clehn8ok/enderwire/STLs/badge_HR.stl

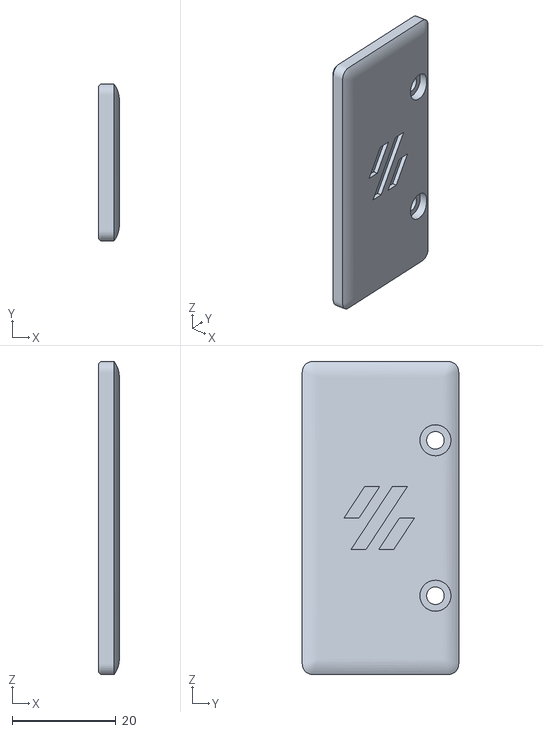
[picture p15: CAD file, 2022-12-23]
STLs/badge_HR.stl
4.00 x 30.2 x 60.4
