clehn8ok/enderwire/STLs/test_print_carriage.stl

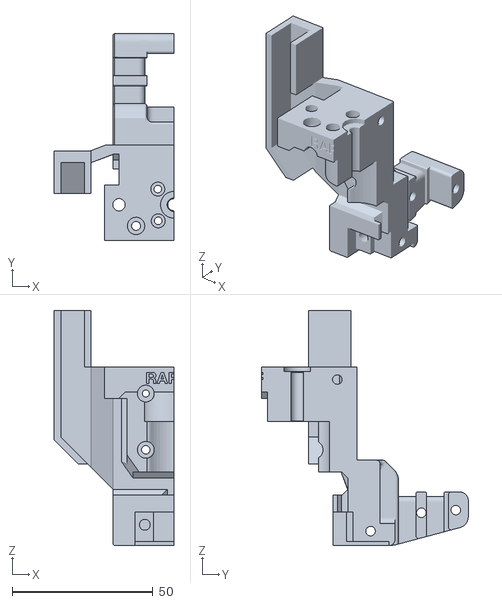
[picture p16: CAD file, 2022-12-23]
STLs/test_print_carriage.stl
42.6 x 73.4 x 83.5
