clehn8ok/enderwire/STLs/x_carriage_3.stl

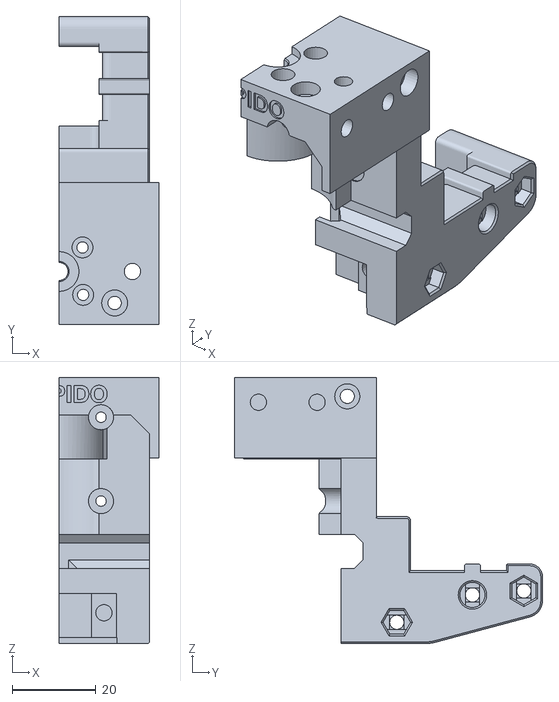
[picture p17: CAD file, 2022-12-23]
STLs/x_carriage_3.stl
23.8 x 73.4 x 63.5
