clehn8ok/enderwire/STLs/y_belt_clamp_K_X_F6RPER4-9665_.stl

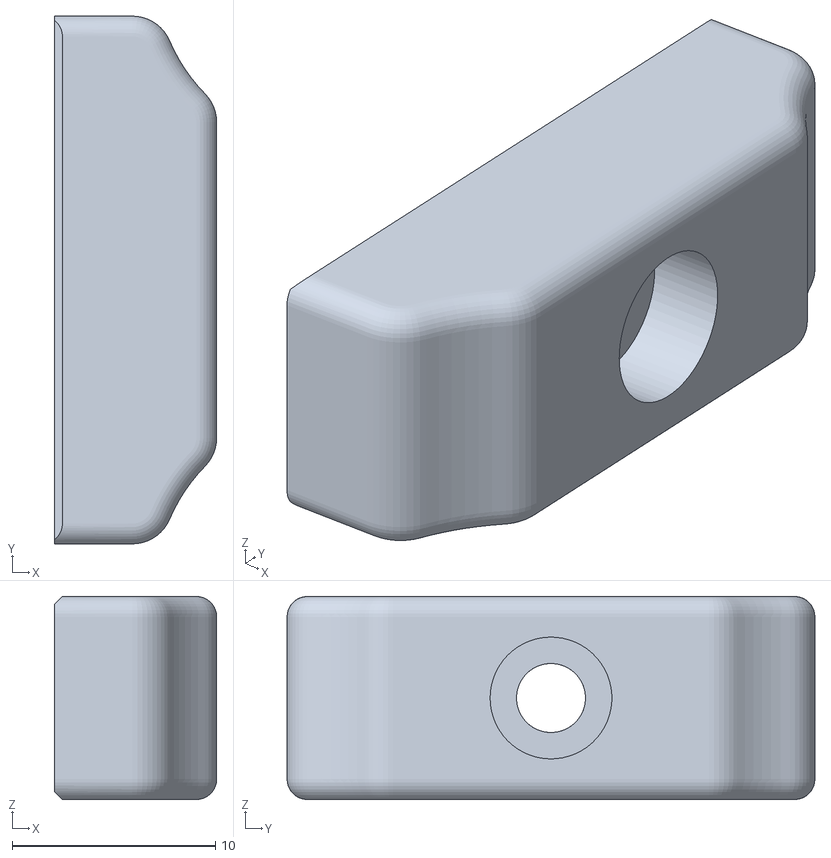
[picture p18: CAD file, 2022-12-23]
STLs/y_belt_clamp_K_X_F6RPER4-9665_.stl
8.00 x 26.0 x 10.0
