clehn8ok/enderwire/STLs/spoolHolder.stl

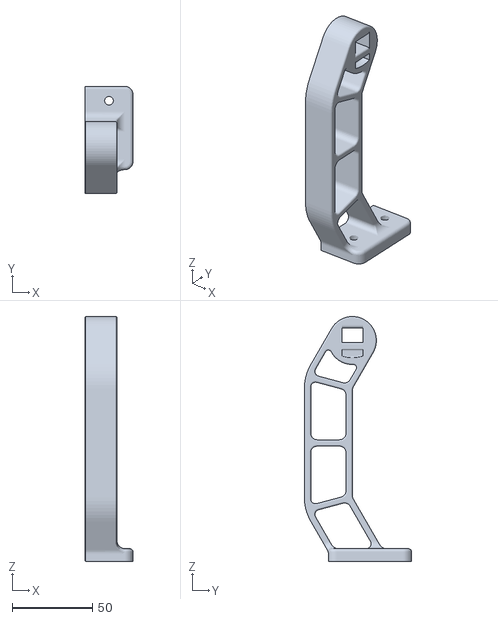
[picture p19: CAD file, 2022-12-23]
STLs/spoolHolder.stl
30.0 x 67.0 x 153.0
