clehn8ok/enderwire/STLs/side_extension_rightlang_hinten.stl

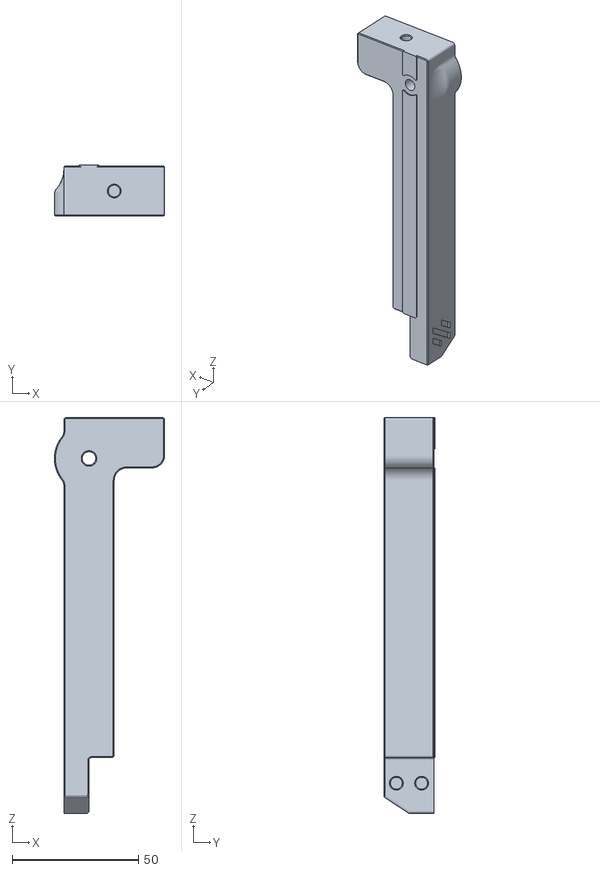
[picture p20: CAD file, 2022-12-23]
STLs/side_extension_rightlang_hinten.stl
43.8 x 20.4 x 157.1
