clehn8ok/enderwire/STLs/knob.stl

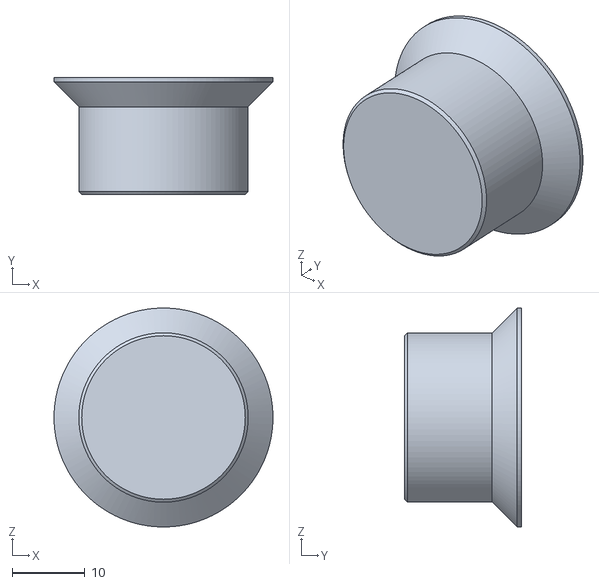
[picture p21: CAD file, 2022-12-23]
STLs/knob.stl
30.0 x 16.0 x 30.0
