clehn8ok/enderwire/STLs/xBlockLH.stl

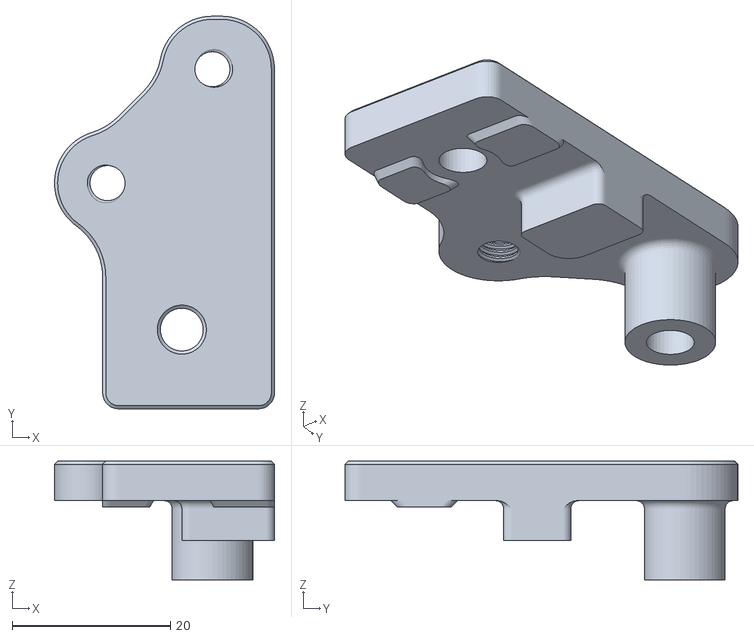
[picture p22: CAD file, 2022-12-23]
STLs/xBlockLH.stl
27.8 x 49.6 x 15.0
