clehn8ok/enderwire/STLs/front_grill_middle.stl

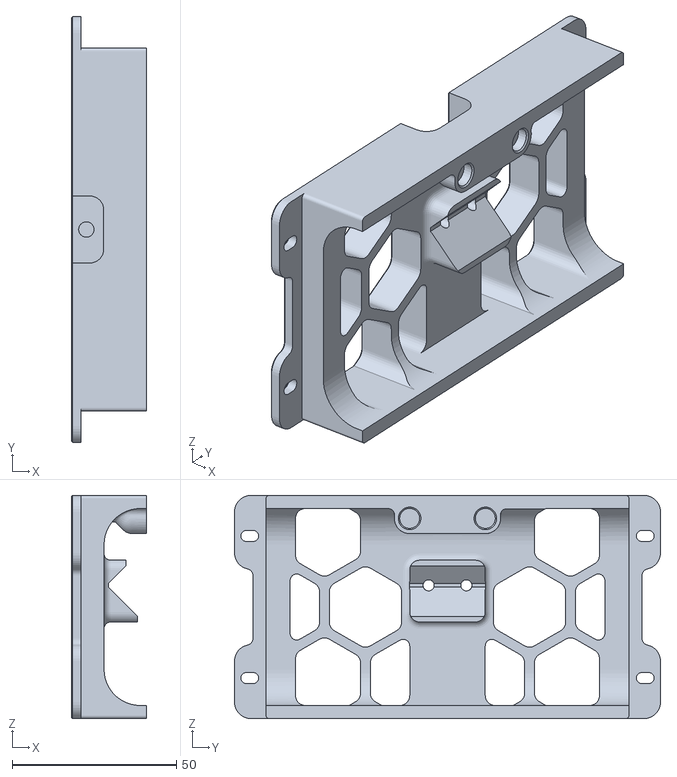
[picture p23: CAD file, 2022-12-23]
STLs/front_grill_middle.stl
23.0 x 129.8 x 68.0
