clehn8ok/enderwire/STLs/sideextension_leftfront.stl

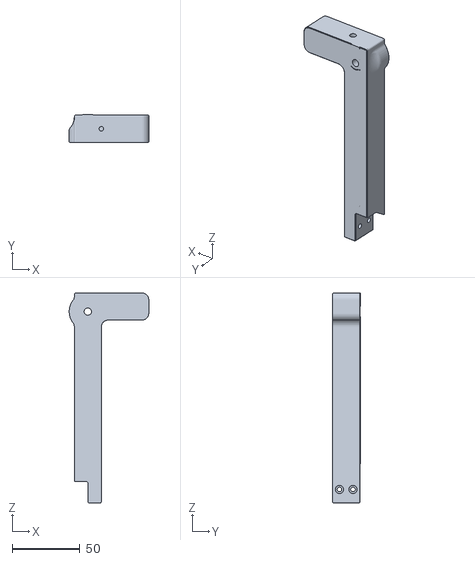
[picture p24: CAD file, 2022-12-23]
STLs/sideextension_leftfront.stl
58.7 x 20.4 x 154.9
