clehn8ok/enderwire/STLs/PI_bracket.stl

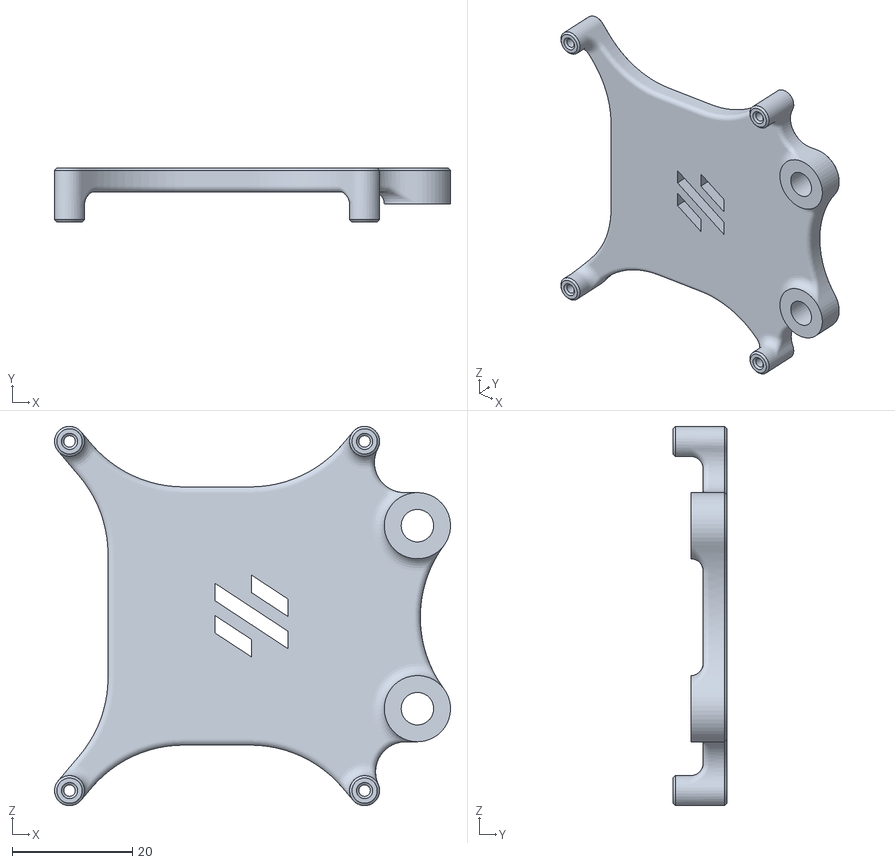
[picture p25: CAD file, 2022-12-23]
STLs/PI_bracket.stl
65.8 x 9.00 x 63.0
