clehn8ok/enderwire/STLs/psuMOunt1.stl

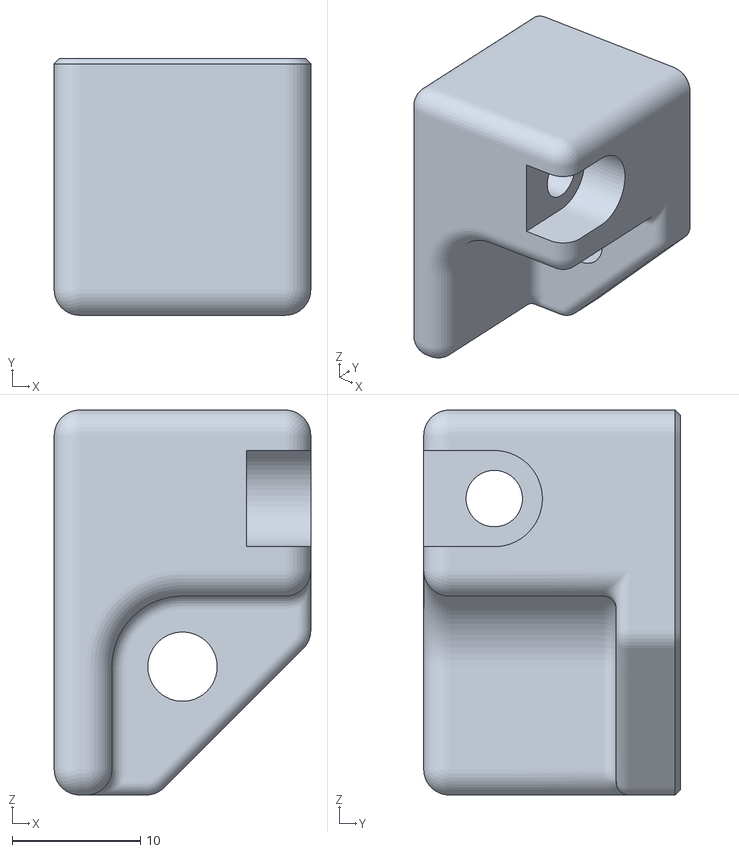
[picture p26: CAD file, 2022-12-23]
STLs/psuMOunt1.stl
20.0 x 20.0 x 30.0
