clehn8ok/enderwire/STLs/displayfront.stl

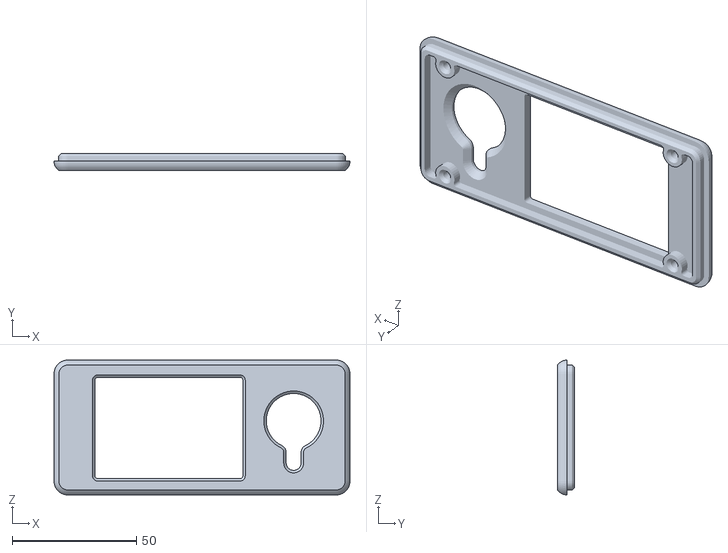
[picture p27: CAD file, 2022-12-23]
STLs/displayfront.stl
119.0 x 7.00 x 54.2
