clehn8ok/enderwire/STLs/connection_plateSideGrill.stl

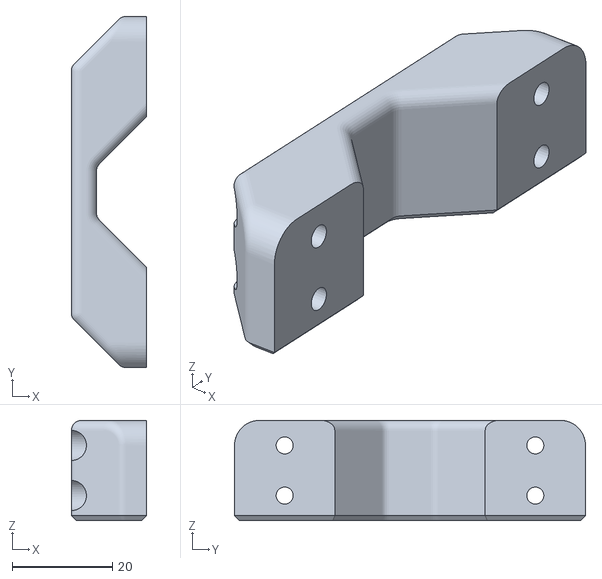
[picture p28: CAD file, 2022-12-23]
STLs/connection_plateSideGrill.stl
15.0 x 70.0 x 20.0
