clehn8ok/enderwire/STLs/zcarriageL.stl

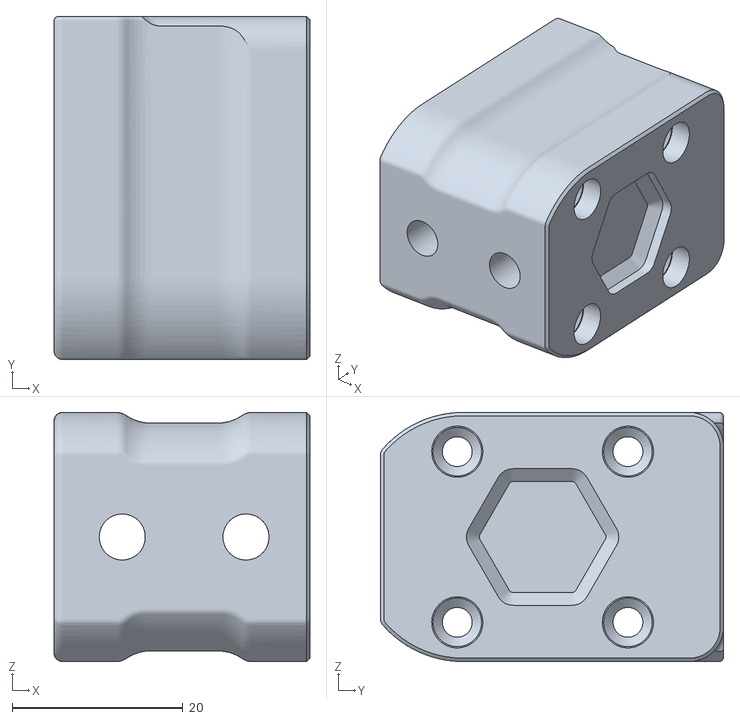
[picture p29: CAD file, 2022-12-23]
STLs/zcarriageL.stl
30.0 x 40.2 x 29.2
