clehn8ok/enderwire/STLs/fron_grill_connector.stl

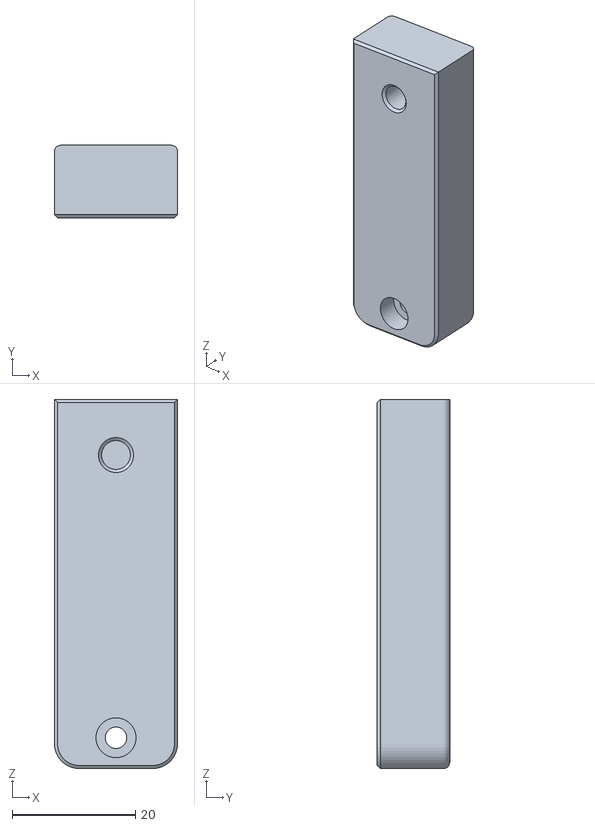
[picture p30: CAD file, 2022-12-23]
STLs/fron_grill_connector.stl
20.0 x 11.8 x 60.0
