clehn8ok/enderwire/STLs/zChainMount.stl

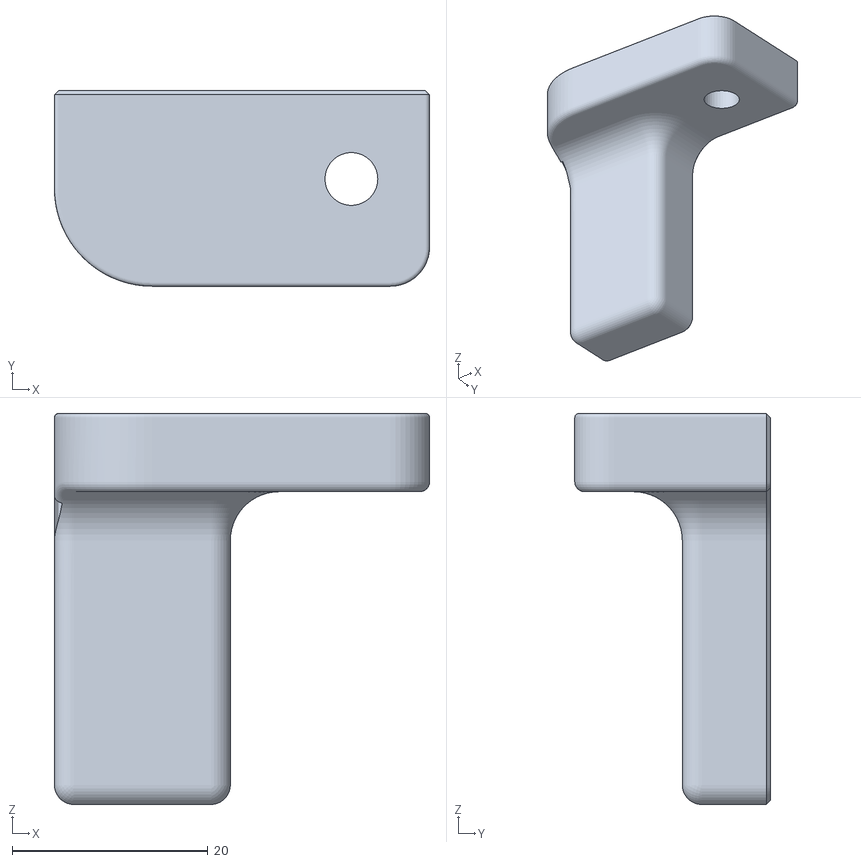
[picture p31: CAD file, 2022-12-23]
STLs/zChainMount.stl
38.4 x 20.0 x 40.0
