clehn8ok/enderwire/STLs/keybak1.stl

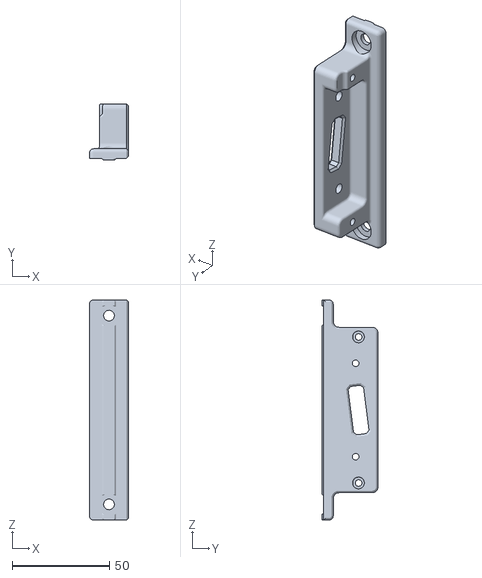
[picture p32: CAD file, 2022-12-23]
STLs/keybak1.stl
20.0 x 28.8 x 113.0
