clehn8ok/enderwire/STLs/displayback.stl

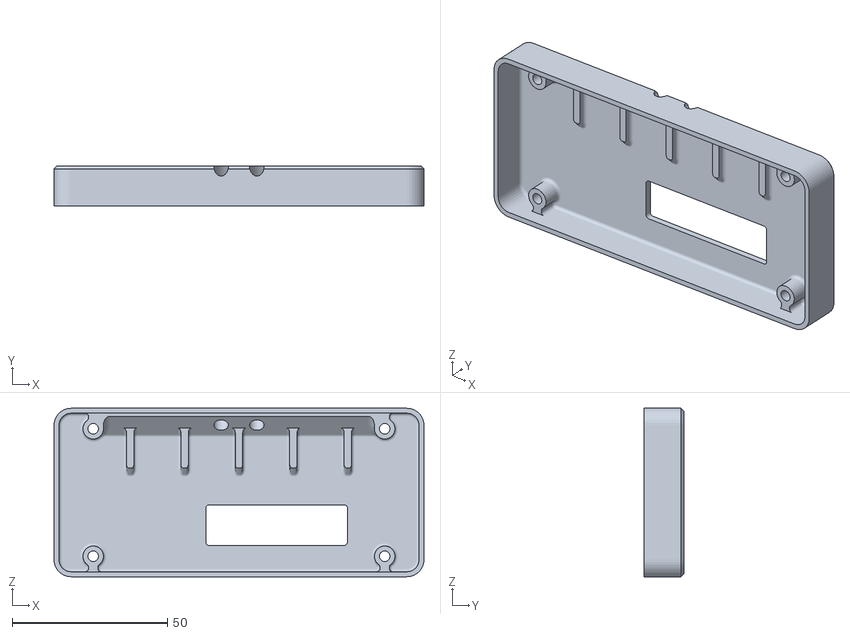
[picture p33: CAD file, 2022-12-23]
STLs/displayback.stl
119.0 x 13.0 x 54.2
