clehn8ok/enderwire/STLs/x_carriage_l.stl

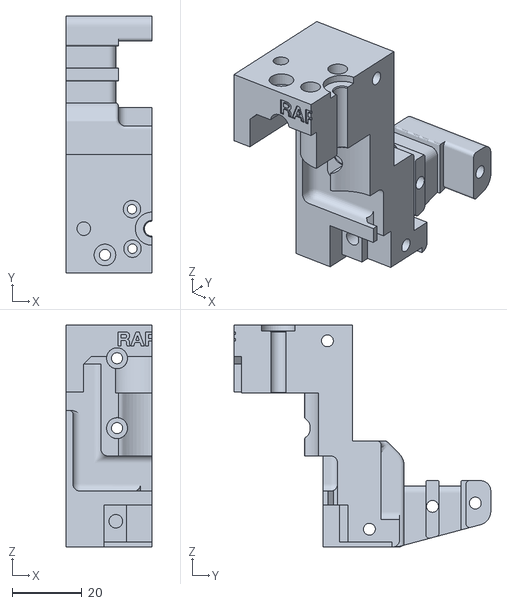
[picture p34: CAD file, 2022-12-23]
STLs/x_carriage_l.stl
24.6 x 73.4 x 63.5
