clehn8ok/enderwire/STLs/z_carriageR.stl

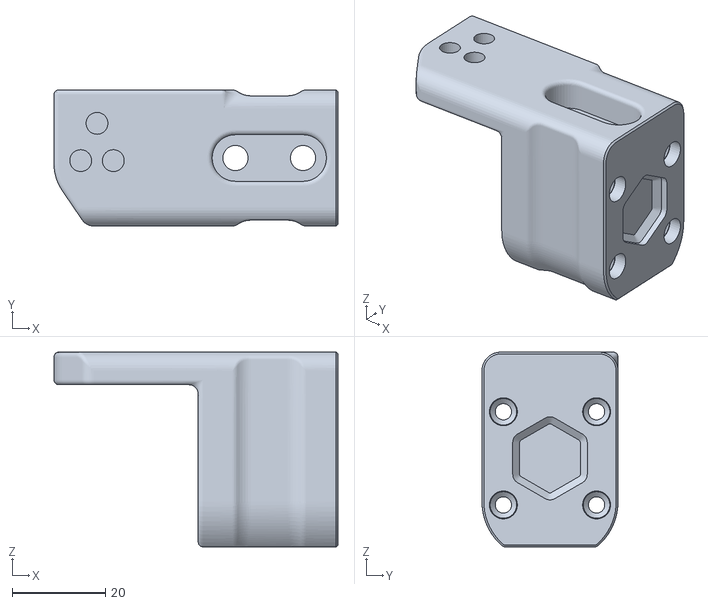
[picture p35: CAD file, 2022-12-23]
STLs/z_carriageR.stl
60.9 x 29.2 x 41.8
