clehn8ok/enderwire/STLs/hing1.stl

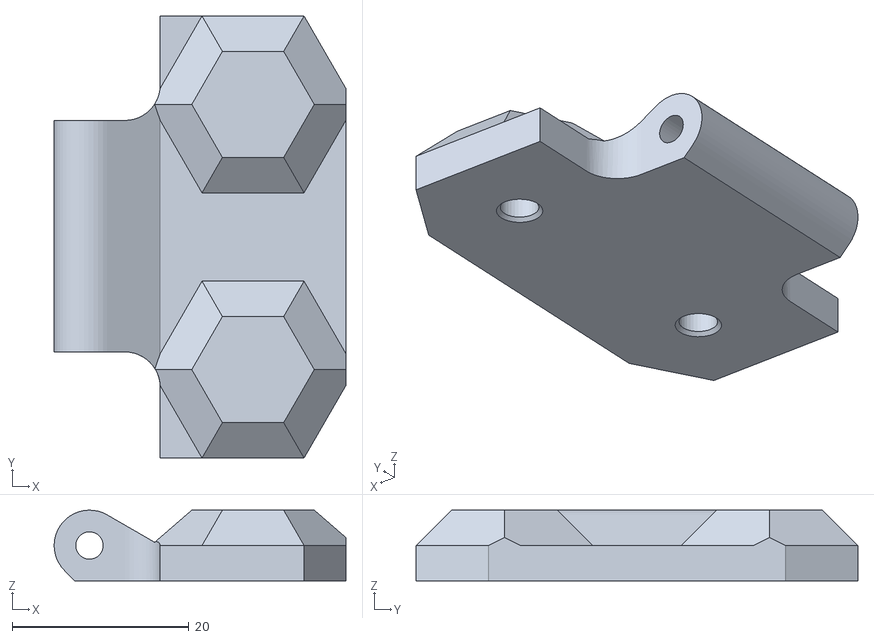
[picture p36: CAD file, 2022-12-23]
STLs/hing1.stl
33.0 x 50.0 x 8.00
