clehn8ok/enderwire/STLs/topDoorRightMagnet.stl

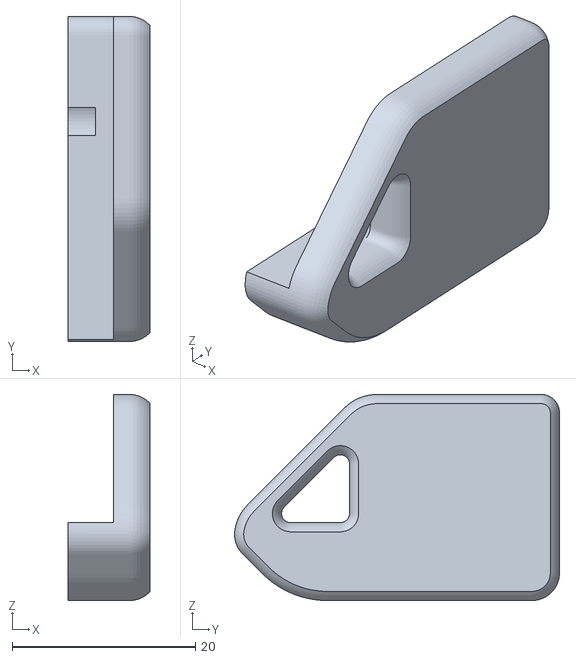
[picture p37: CAD file, 2022-12-23]
STLs/topDoorRightMagnet.stl
9.00 x 35.5 x 22.5
