clehn8ok/enderwire/STLs/side_extension_rightlang_vorne.stl

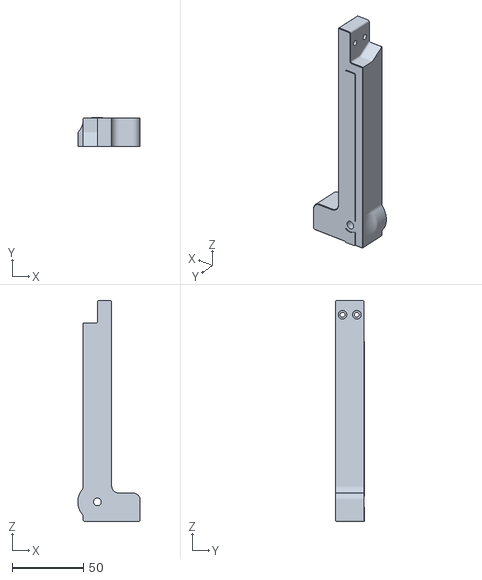
[picture p38: CAD file, 2022-12-23]
STLs/side_extension_rightlang_vorne.stl
43.8 x 20.4 x 154.9
