clehn8ok/enderwire/STLs/sideextension_rioghtfrontBreit_Vorne.stl

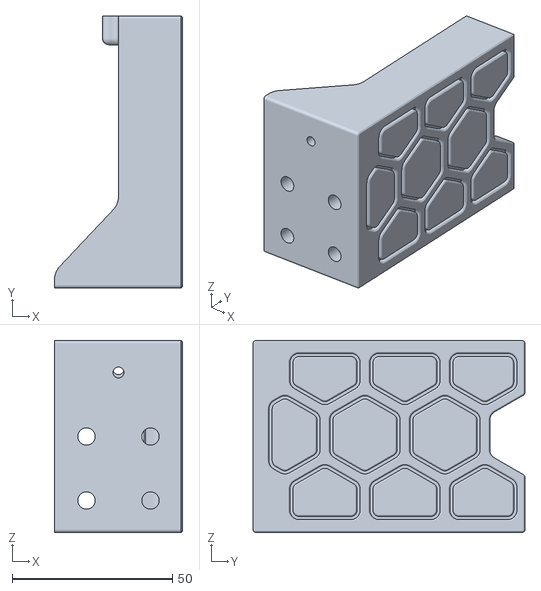
[picture p39: CAD file, 2022-12-23]
STLs/sideextension_rioghtfrontBreit_Vorne.stl
40.0 x 85.0 x 60.0
