clehn8ok/enderwire/STLs/y_axis_tensioner_K_X_F6RPER3-9642_.stl

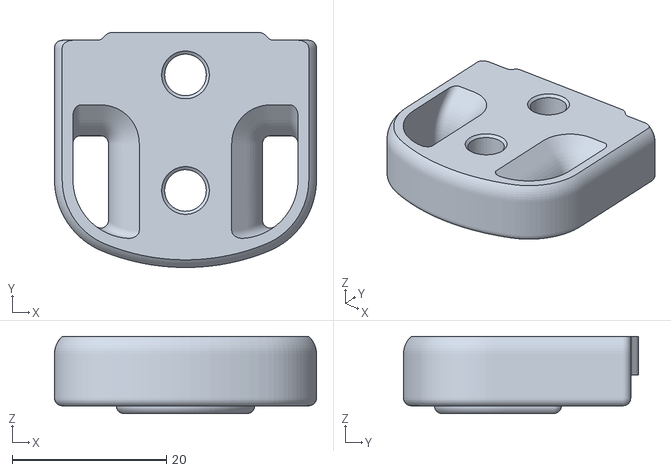
[picture p40: CAD file, 2022-12-23]
STLs/y_axis_tensioner_K_X_F6RPER3-9642_.stl
34.0 x 30.5 x 10.0
