clehn8ok/enderwire/STLs/ledHolder_upperright.stl

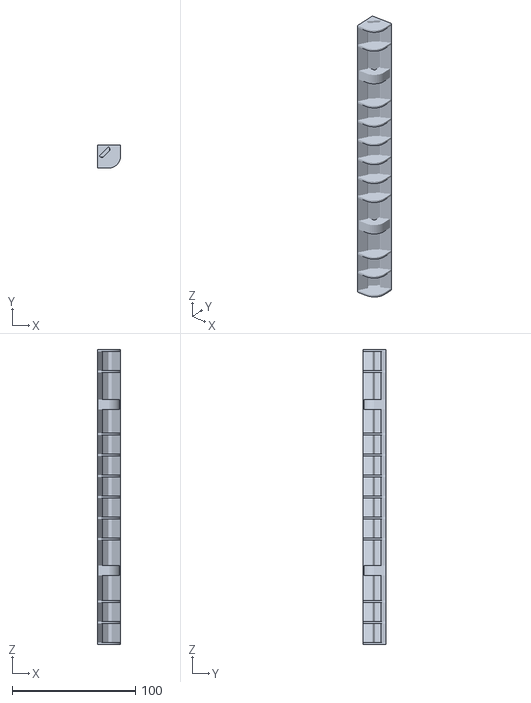
[picture p41: CAD file, 2022-12-23]
STLs/ledHolder_upperright.stl
19.0 x 19.0 x 239.6
