clehn8ok/enderwire/STLs/backacrylPanelHolder.stl

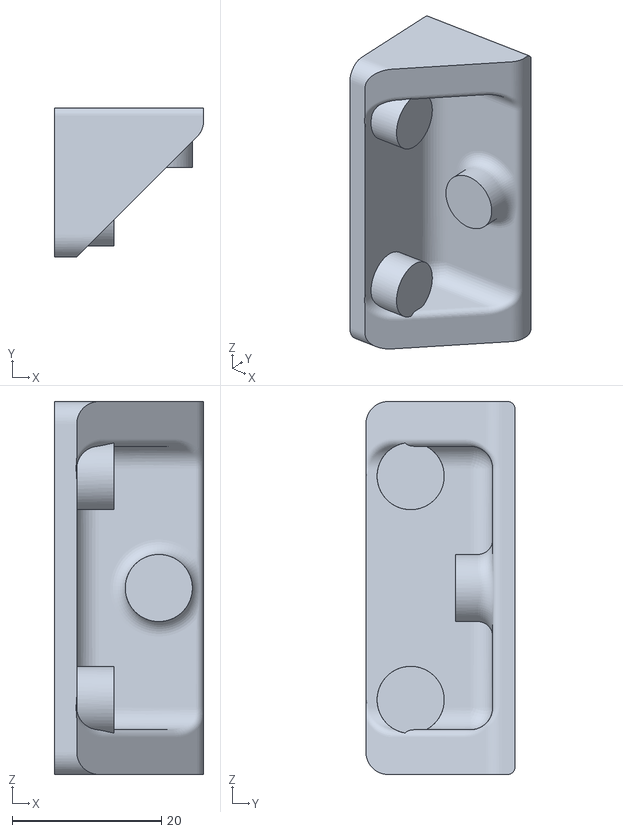
[picture p42: CAD file, 2022-12-23]
STLs/backacrylPanelHolder.stl
20.0 x 20.0 x 50.0
