clehn8ok/enderwire/STLs/Idler_mount.stl

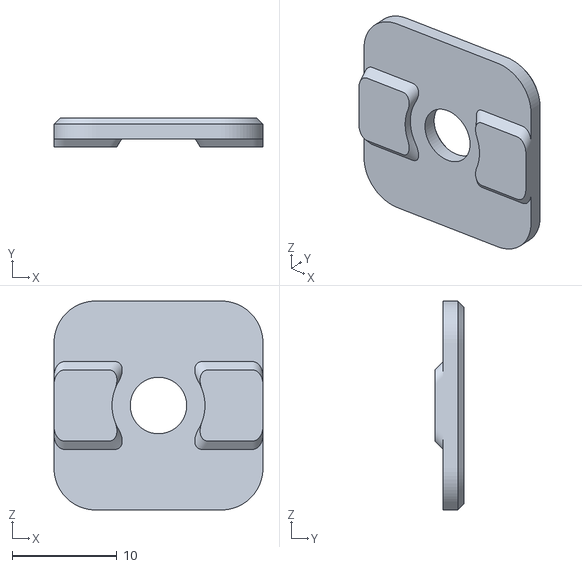
[picture p43: CAD file, 2022-12-23]
STLs/Idler_mount.stl
20.0 x 2.80 x 20.0
