clehn8ok/enderwire/STLs/front_extension_vornerechts.stl

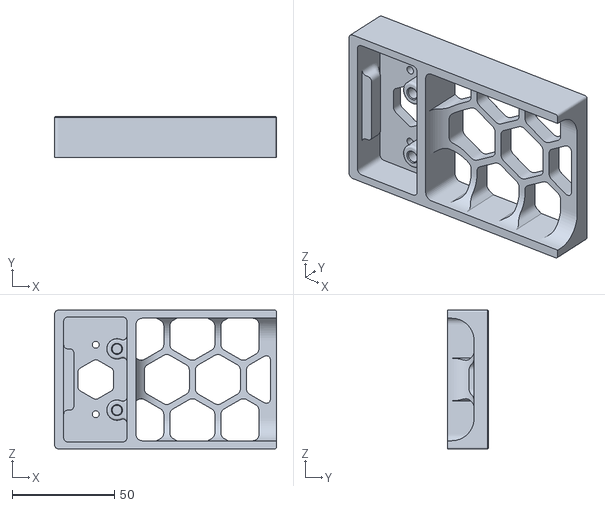
[picture p44: CAD file, 2022-12-23]
STLs/front_extension_vornerechts.stl
108.7 x 20.0 x 68.0
