clehn8ok/enderwire/STLs/skr_miniMount.stl

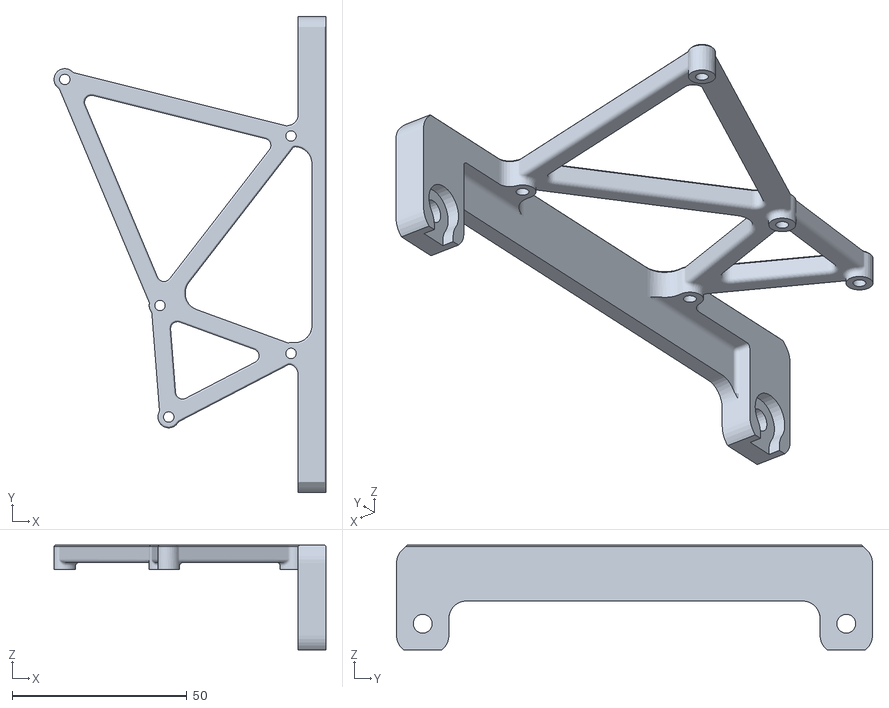
[picture p45: CAD file, 2022-12-23]
STLs/skr_miniMount.stl
77.8 x 136.2 x 30.0
