clehn8ok/enderwire/STLs/enclosureClip_L.stl

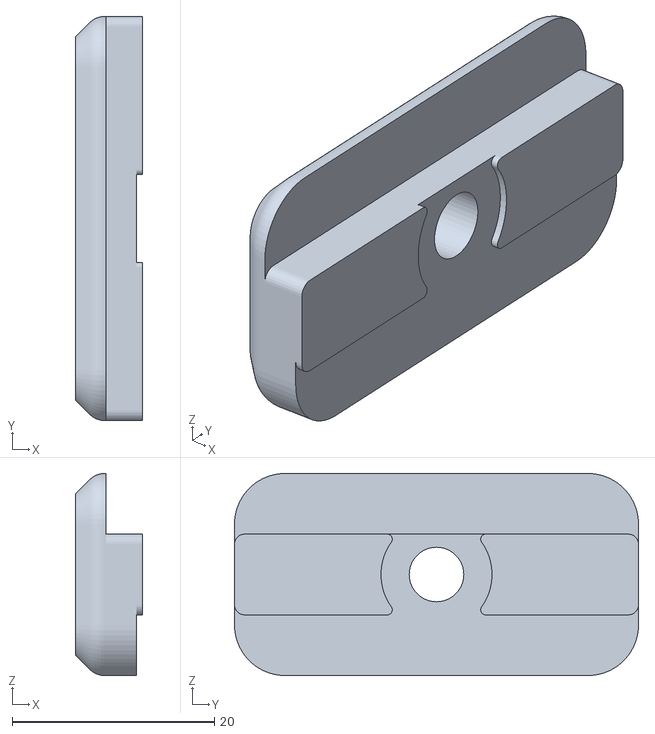
[picture p46: CAD file, 2022-12-23]
STLs/enclosureClip_L.stl
6.60 x 40.0 x 20.0
