clehn8ok/enderwire/STLs/rightMotormount_moreNarrow_avoidBeltRubbing.stl

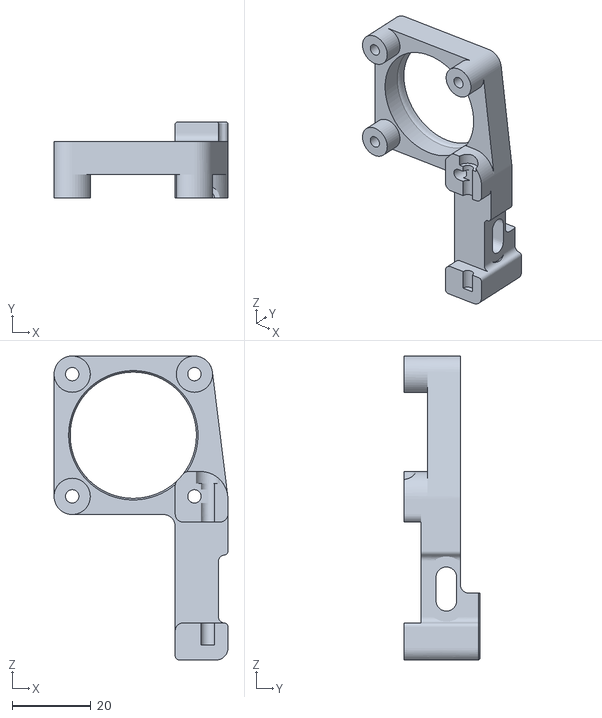
[picture p47: CAD file, 2022-12-23]
STLs/rightMotormount_moreNarrow_avoidBeltRubbing.stl
44.1 x 19.4 x 77.1
