clehn8ok/enderwire/STLs/cablerelief_new.stl

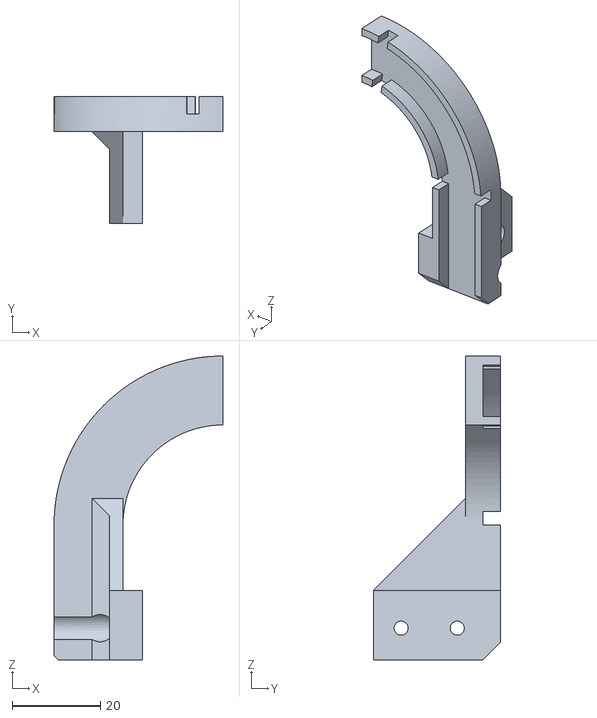
[picture p48: CAD file, 2022-12-23]
STLs/cablerelief_new.stl
38.2 x 28.8 x 68.8
