clehn8ok/enderwire/STLs/z_chain_mountFrame.stl

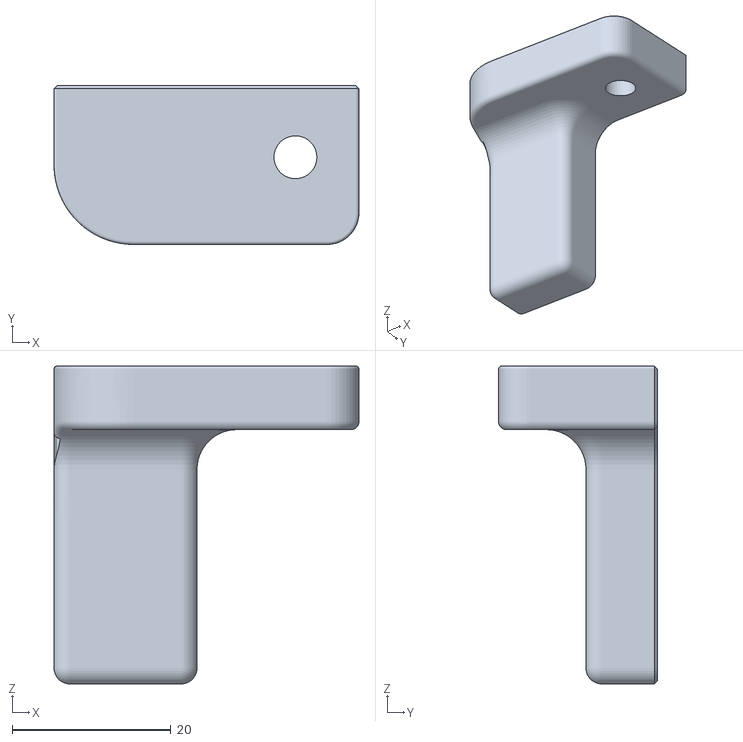
[picture p49: CAD file, 2022-12-23]
STLs/z_chain_mountFrame.stl
38.4 x 20.0 x 40.0
