clehn8ok/enderwire/STLs/xBlockL.stl

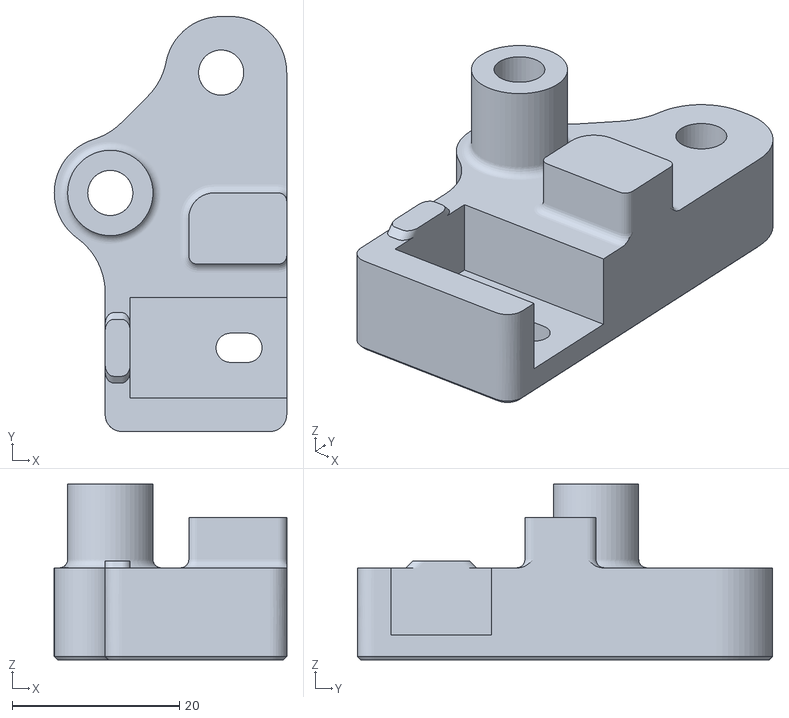
[picture p50: CAD file, 2022-12-23]
STLs/xBlockL.stl
27.8 x 49.6 x 21.0
