clehn8ok/enderwire/STLs/piPsu.stl

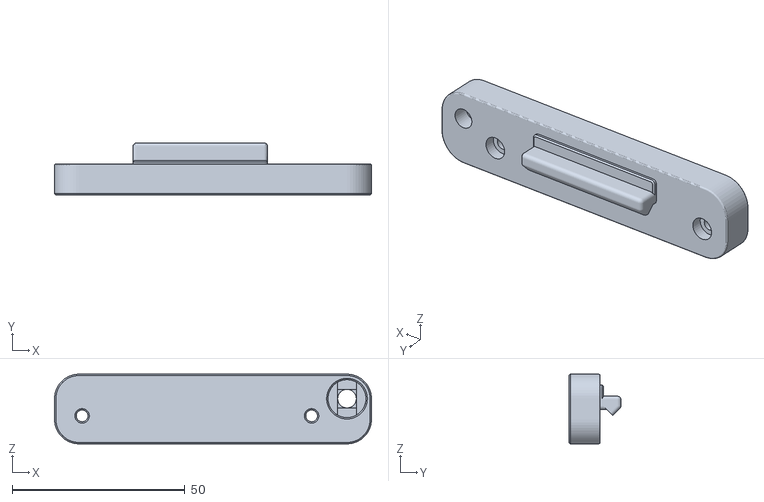
[picture p51: CAD file, 2022-12-23]
STLs/piPsu.stl
91.8 x 15.1 x 20.2
