clehn8ok/enderwire/STLs/keybak2.stl

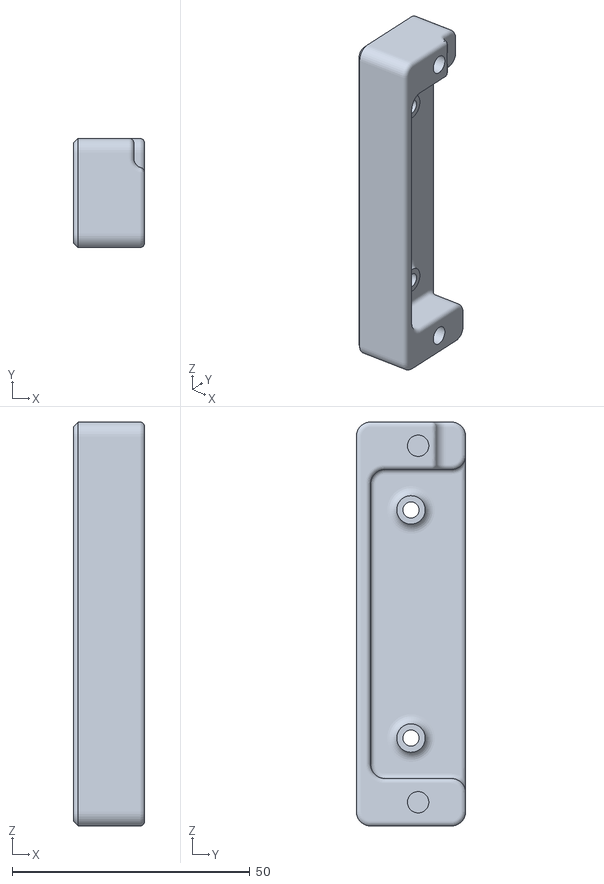
[picture p52: CAD file, 2022-12-23]
STLs/keybak2.stl
15.0 x 23.0 x 85.0
