clehn8ok/enderwire/STLs/hinge1.stl

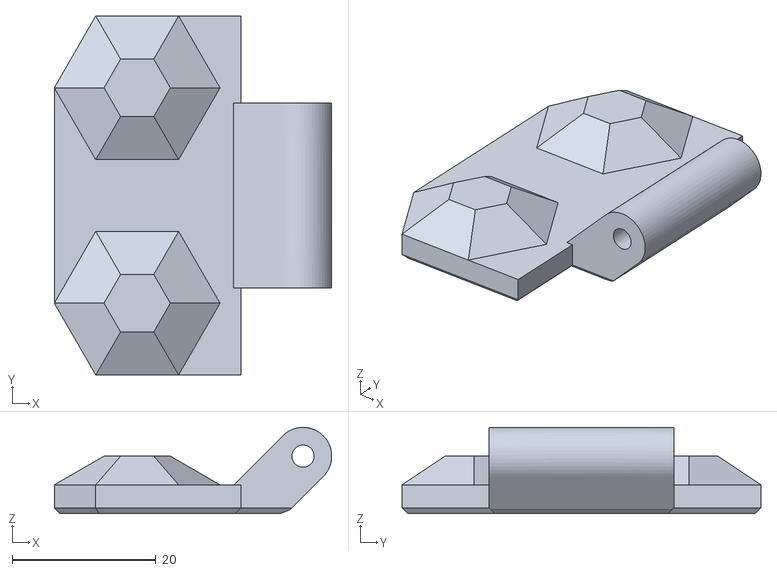
[picture p53: CAD file, 2022-12-23]
STLs/hinge1.stl
38.6 x 50.0 x 12.0
