clehn8ok/enderwire/STLs/spoolHolder_2.stl

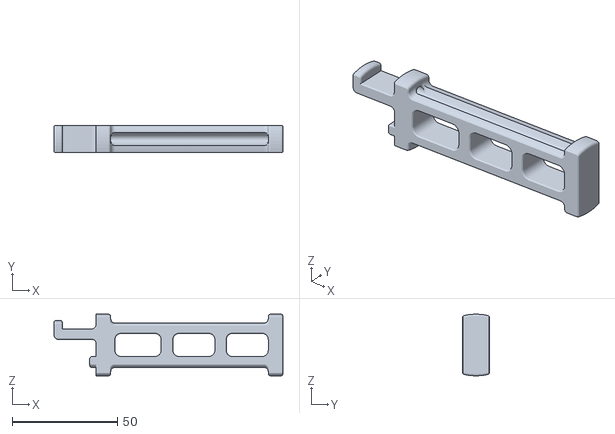
[picture p54: CAD file, 2022-12-23]
STLs/spoolHolder_2.stl
109.0 x 13.0 x 29.4
