clehn8ok/enderwire/STLs/cablerelief.stl

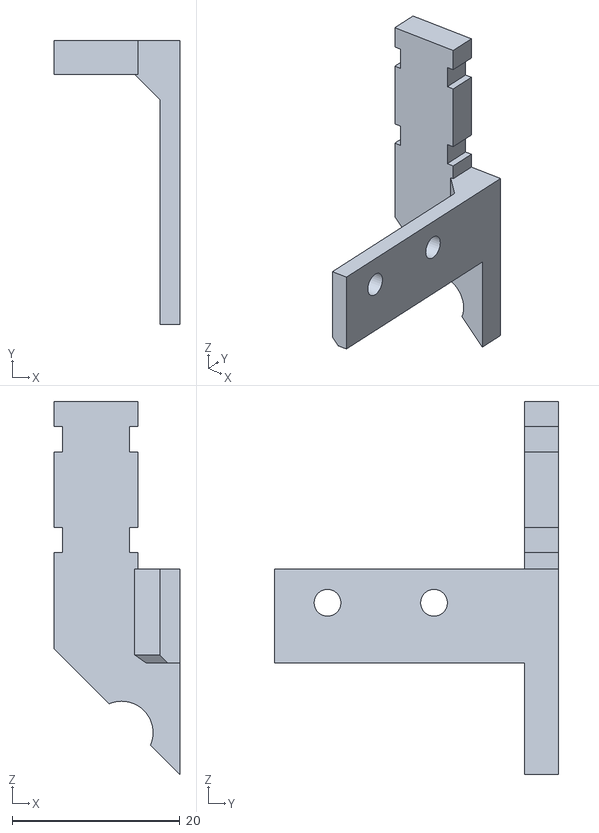
[picture p55: CAD file, 2022-12-23]
STLs/cablerelief.stl
15.0 x 33.8 x 44.5
