clehn8ok/enderwire/STLs/toolhead_fanduct.stl

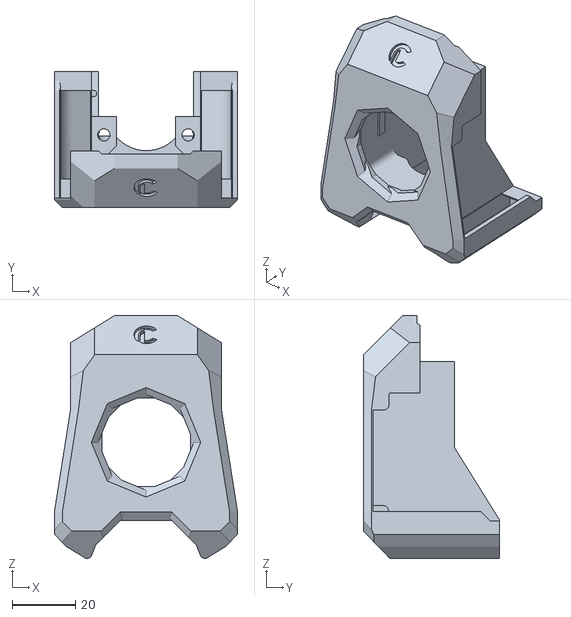
[picture p56: CAD file, 2022-12-23]
STLs/toolhead_fanduct.stl
57.9 x 43.0 x 76.9
