clehn8ok/enderwire/STLs/y_endstopHolder_K_X_F6RPER4-9665_.stl

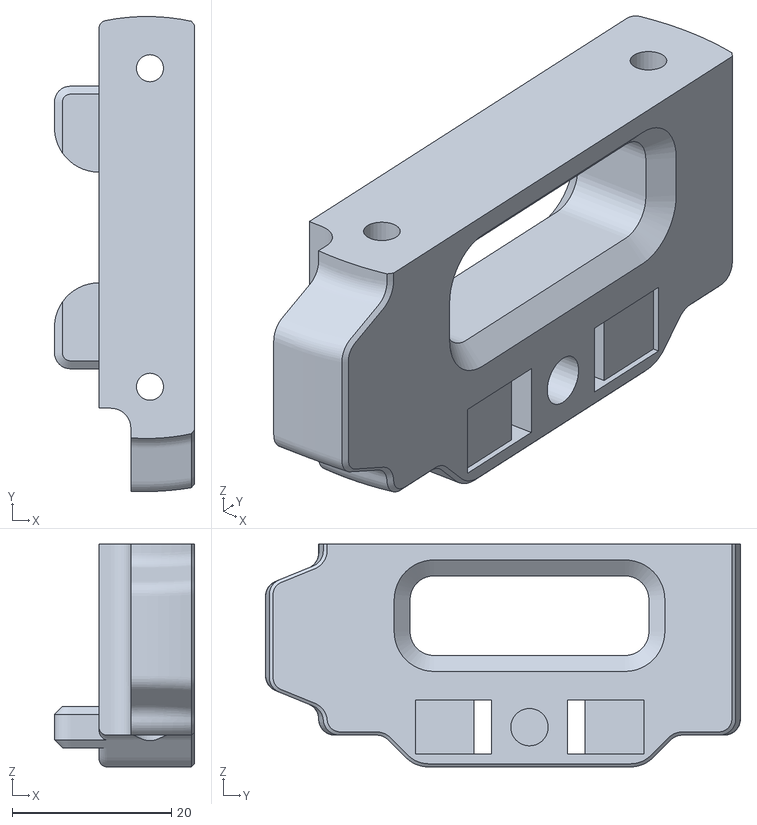
[picture p57: CAD file, 2022-12-23]
STLs/y_endstopHolder_K_X_F6RPER4-9665_.stl
17.6 x 59.7 x 28.0
