clehn8ok/enderwire/STLs/x_carriage_r.stl

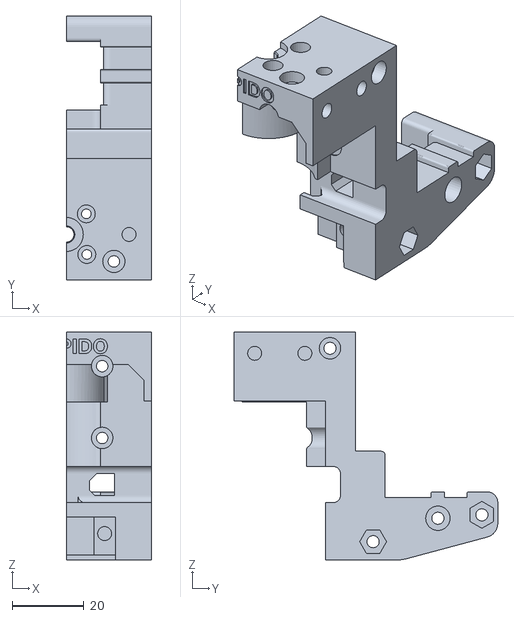
[picture p58: CAD file, 2022-12-23]
STLs/x_carriage_r.stl
23.8 x 73.4 x 63.5
