clehn8ok/enderwire/STLs/z_carriageL_keybak.stl

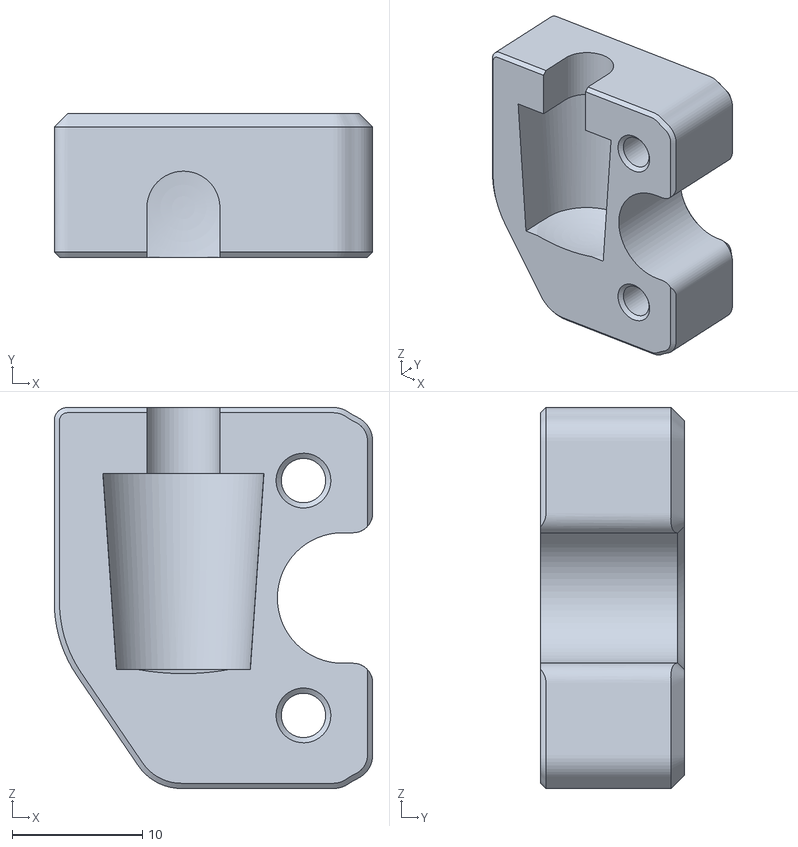
[picture p59: CAD file, 2022-12-23]
STLs/z_carriageL_keybak.stl
24.4 x 11.0 x 29.2
