clehn8ok/enderwire/STLs/rearGrill_fan.stl

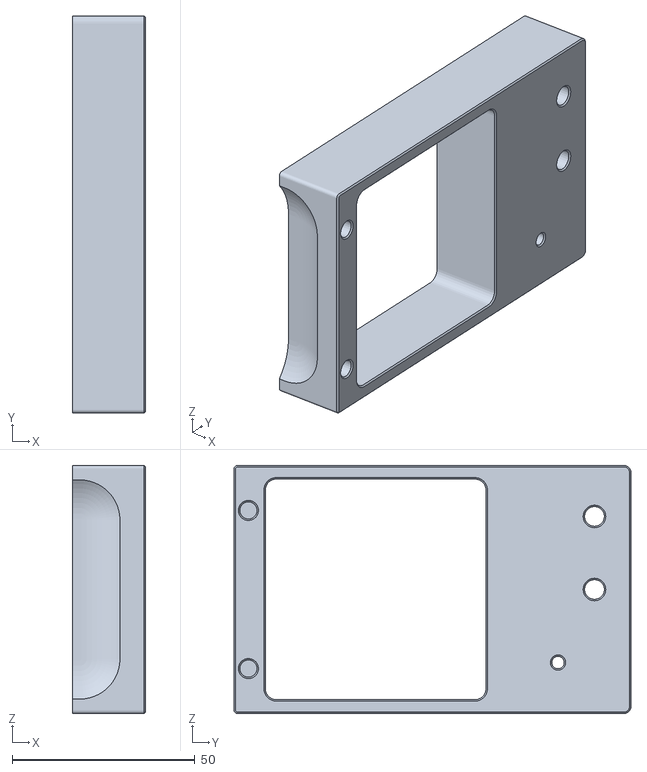
[picture p60: CAD file, 2022-12-23]
STLs/rearGrill_fan.stl
20.0 x 108.7 x 68.0
