clehn8ok/enderwire/STLs/y_chaninMount.stl

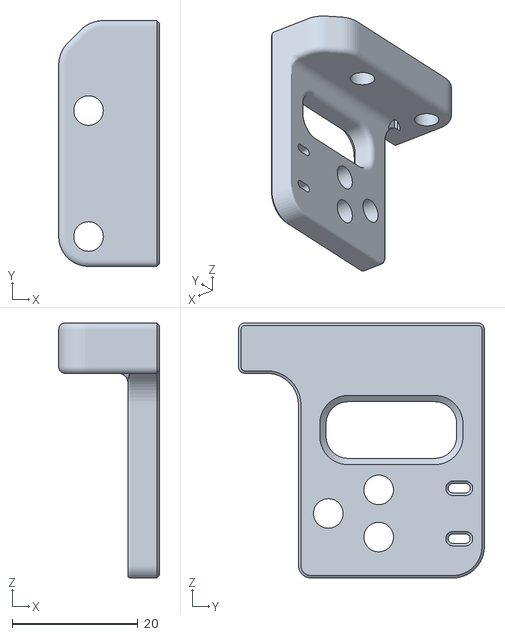
[picture p61: CAD file, 2022-12-23]
STLs/y_chaninMount.stl
16.0 x 39.0 x 40.5
