clehn8ok/enderwire/STLs/y_motorMount.stl

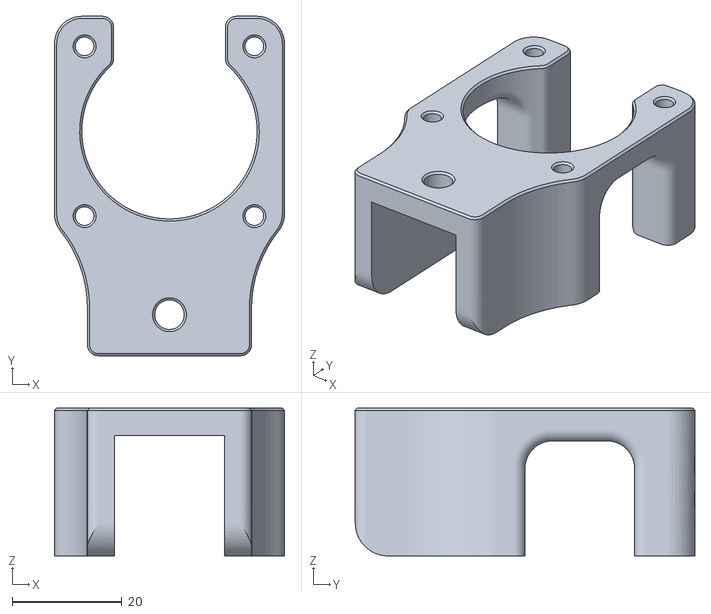
[picture p62: CAD file, 2022-12-23]
STLs/y_motorMount.stl
42.0 x 62.0 x 27.0
