clehn8ok/enderwire/STLs/BL_touchHOlder.stl

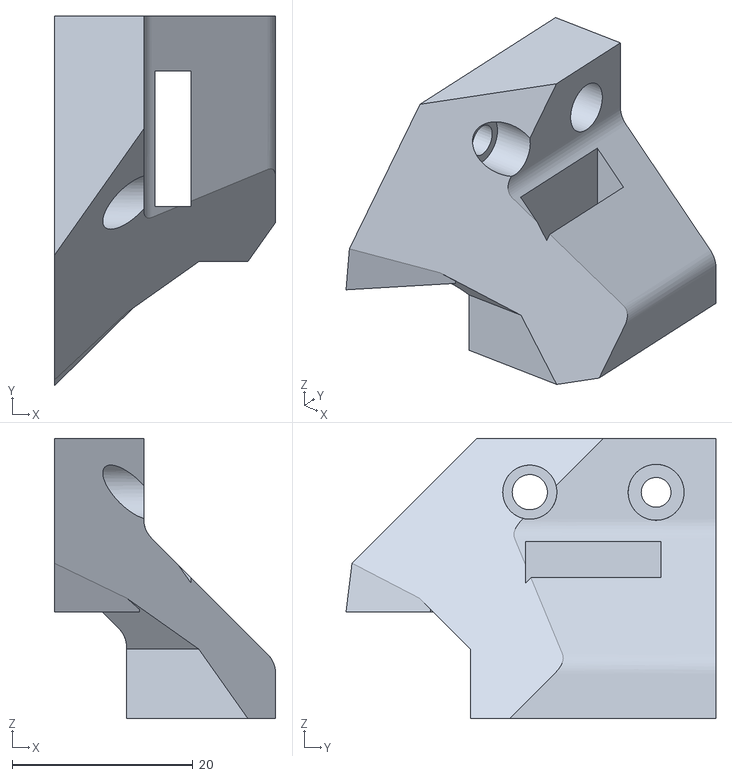
[picture p63: CAD file, 2022-12-23]
STLs/BL_touchHOlder.stl
24.5 x 41.0 x 31.0
