clehn8ok/enderwire/STLs/klickyWired#.stl

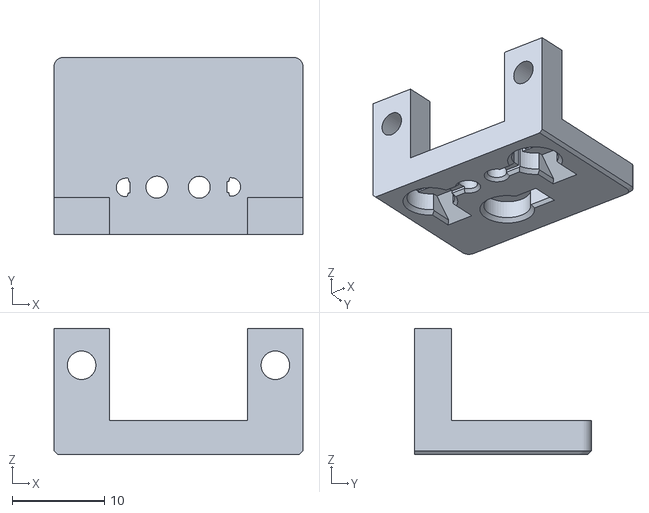
[picture p64: CAD file, 2022-12-23]
STLs/klickyWired#.stl
27.0 x 19.2 x 13.7
